kinoshita-lab/StemsMIDI/soft/StemsMIDI/src/stemsmidi_switch.hpp

#pragma once
#ifndef STEMSMIDI_SWITCH_HPP
#define STEMSMIDI_SWITCH_HPP

#include <cstdint>
#include <cstdlib>
#include <Arduino.h>
namespace kinoshita_lab
{
namespace stemsmidi
{

template <uint8_t num_switches, uint8_t scan_period>
class Switchs
{
public:
    typedef void (*SwitchHandler)(uint32_t switch_index, const int off_on);

    enum InternalState
    {
        Init,
        LoadStart,
        ReadEachBits,
        WaitNext,
        NumNormalStates,
        UnknownState = 0xff,
    };

    Switchs(
        const uint8_t npl_pin, const uint8_t clock_pin,
        const uint8_t output_pin, SwitchHandler handler = nullptr)
        : pins_(npl_pin, clock_pin, output_pin),
          handler_(handler)
    {

        // initialize switch status
        for (auto i = 0u; i < num_switches; ++i) {
            scan_buffers_[i]        = 1;
            former_scan_buffers_[i] = 1;
            switch_status_[i]       = 1;
        }
        pinMode(npl_pin, OUTPUT);
        pinMode(clock_pin, OUTPUT);
        pinMode(output_pin, INPUT_PULLUP);

        setState(Init);
    }

    void setHandler(SwitchHandler handler)
    {
        handler_ = handler;
    }

    virtual ~Switchs()
    {
    }

    void update()
    {
        switch (status_) {
        case Init:
            setState(LoadStart);
            break;
        case LoadStart:
            setState(ReadEachBits);
            break;
        case ReadEachBits: {
            for (auto ic_index = 0u; ic_index < num_switches / 8; ic_index++) {
                constexpr auto num_bits = 8;
                for (auto i = 0u; i < num_bits; ++i) {
                    digitalWrite(pins_.clock_pin, LOW);
                    const auto read_data                                    = digitalRead(pins_.output_pin);
                    scan_buffers_[(ic_index * num_bits) + num_bits - i - 1] = read_data;
                    digitalWrite(pins_.clock_pin, HIGH);
                }
            }
            updateSwitchStatus();
            setState(WaitNext);
            break;
        case WaitNext: {
            const auto current = millis();
            const auto delta   = current - wait_start_;
            if (delta >= scan_period) {
                setState(LoadStart);
            }
        } break;
        default:
            break;
        }
        }
    };

    void forceScan()
    {
        // scan 2 times just in case for robustness
        for (auto i = 0; i < 4; ++i) {
            for (auto i = 0; i < NumNormalStates; ++i) {
                update();
                delay(scan_period);
            }
        }
    }

    bool switchIsOn(const uint32_t switch_index) const
    {
        if (switch_index >= num_switches) {
            return false;
        }

        return switch_status_[switch_index] == 0;
    }

protected:
    uint8_t status_          = UnknownState;
    size_t will_read_switch_ = 0;

    void setState(const int status)
    {
        status_ = status;
        assert(pins_.npl_pin != Pins::INVALID_PIN_CONFIGURATION);
        assert(pins_.clock_pin != Pins::INVALID_PIN_CONFIGURATION);
        assert(pins_.output_pin != Pins::INVALID_PIN_CONFIGURATION);

        switch (status_) {
        case Init:
            digitalWrite(pins_.npl_pin, HIGH);
            digitalWrite(pins_.clock_pin, LOW);
            break;
        case LoadStart:
            digitalWrite(pins_.npl_pin, LOW);
            digitalWrite(pins_.clock_pin, LOW);
            will_read_switch_ = 0;
            break;
        case ReadEachBits:
            digitalWrite(pins_.clock_pin, LOW);
            digitalWrite(pins_.npl_pin, HIGH);
            break;
        case WaitNext:
            wait_start_ = millis();
            digitalWrite(pins_.npl_pin, HIGH);
            digitalWrite(pins_.clock_pin, LOW);
            break;
        default:
            break;
        }
    }

    void updateSwitchStatus()
    {
        for (auto i = 0u; i < num_switches; ++i) {
            if (scan_buffers_[i] == former_scan_buffers_[i]) {
                const auto new_status = scan_buffers_[i];
                auto current_status   = switch_status_[i];
                if (current_status != new_status) {
                    switch_status_[i] = (new_status);

                    const auto notification_status = !switch_status_[i]; // NOTE: inverted!! off = HIGH, on = LOW
                    if (handler_) {
                        (*handler_)(i, notification_status);
                    }
                }
            }
            former_scan_buffers_[i] = scan_buffers_[i];
        }
    }
    struct Pins
    {
        enum
        {
            INVALID_PIN_CONFIGURATION = 0xff,
        };
        Pins(const uint8_t npl_pin, const uint8_t clock_pin,
             const uint8_t input_pin)
            : npl_pin(npl_pin), clock_pin(clock_pin), output_pin(input_pin) {}

        Pins() = default;

        uint8_t npl_pin    = INVALID_PIN_CONFIGURATION;
        uint8_t clock_pin  = INVALID_PIN_CONFIGURATION;
        uint8_t output_pin = INVALID_PIN_CONFIGURATION;
    };
    Pins pins_;
    SwitchHandler handler_ = nullptr;

    uint8_t scan_buffers_[num_switches]        = {0};
    uint8_t former_scan_buffers_[num_switches] = {0};
    uint8_t switch_status_[num_switches]       = {0};
    uint32_t wait_start_                       = 0;

private:
    Switchs(const Switchs&) {}
};
} // namespace stemsmidi
} // namespace kinoshita_lab

#endif // STEMSMIDI_SWITCH_HPP
