kinoshita-lab/StemsMIDI/soft/StemsMIDI/src/stemsmidi_cc_numbers.h

#pragma once
#ifndef STEMSMIDI_CC_NUMBERS_H
#define STEMSMIDI_CC_NUMBERS_H

namespace kinoshita_lab
{
namespace stemsmidi
{
namespace cc_numbers
{
enum
{
    kDeckA_Slot1_Volume_Adjust = 10,
    kDeckA_Slot1_Mute_OnOff    = 11,
    kDeckA_Slot1_Filter_Adjust = 12,
    kDeckA_Slot1_Filter_OnOff  = 13,
    kDeckA_Slot1_FxSend_Adjust = 14,
    kDeckA_Slot1_FxSend_OnOff  = 15,

    kDeckA_Slot2_Volume_Adjust = 16,
    kDeckA_Slot2_Mute_OnOff    = 17,
    kDeckA_Slot2_Filter_Adjust = 18,
    kDeckA_Slot2_Filter_OnOff  = 19,
    kDeckA_Slot2_FxSend_Adjust = 20,
    kDeckA_Slot2_FxSend_OnOff  = 21,

    kDeckA_Slot3_Volume_Adjust = 22,
    kDeckA_Slot3_Mute_OnOff    = 23,
    kDeckA_Slot3_Filter_Adjust = 24,
    kDeckA_Slot3_Filter_OnOff  = 25,
    kDeckA_Slot3_FxSend_Adjust = 26,
    kDeckA_Slot3_FxSend_OnOff  = 27,

    kDeckA_Slot4_Volume_Adjust = 28,
    kDeckA_Slot4_Mute_OnOff    = 29,
    kDeckA_Slot4_Filter_Adjust = 30,
    kDeckA_Slot4_Filter_OnOff  = 31,
    kDeckA_Slot4_FxSend_Adjust = 32,
    kDeckA_Slot4_FxSend_OnOff  = 33,

    kDeckB_Slot1_Volume_Adjust = 40,
    kDeckB_Slot1_Mute_OnOff    = 41,
    kDeckB_Slot1_Filter_Adjust = 42,
    kDeckB_Slot1_Filter_OnOff  = 43,
    kDeckB_Slot1_FxSend_Adjust = 44,
    kDeckB_Slot1_FxSend_OnOff  = 45,

    kDeckB_Slot2_Volume_Adjust = 46,
    kDeckB_Slot2_Mute_OnOff    = 47,
    kDeckB_Slot2_Filter_Adjust = 48,
    kDeckB_Slot2_Filter_OnOff  = 49,
    kDeckB_Slot2_FxSend_Adjust = 50,
    kDeckB_Slot2_FxSend_OnOff  = 51,

    kDeckB_Slot3_Volume_Adjust = 52,
    kDeckB_Slot3_Mute_OnOff    = 53,
    kDeckB_Slot3_Filter_Adjust = 54,
    kDeckB_Slot3_Filter_OnOff  = 55,
    kDeckB_Slot3_FxSend_Adjust = 56,
    kDeckB_Slot3_FxSend_OnOff  = 57,

    kDeckB_Slot4_Volume_Adjust = 58,
    kDeckB_Slot4_Mute_OnOff    = 59,
    kDeckB_Slot4_Filter_Adjust = 60,
    kDeckB_Slot4_Filter_OnOff  = 61,
    kDeckB_Slot4_FxSend_Adjust = 62,
    kDeckB_Slot4_FxSend_OnOff  = 63,
};

} // namespace cc_numbers
} // namespace stemsmidi
} // namespace kinoshita_lab

#endif // STEMSMIDI_CC_NUMBERS_H
