kinoshita-lab/StemsMIDI/soft/StemsMIDI/src/stemsmidi_switch_ids.h

#pragma once
#ifndef STEMSMIDI_SWITCH_IDS_H
#define STEMSMIDI_SWITCH_IDS_H

namespace kinoshita_lab
{
namespace stemsmidi
{
enum SwitchId
{
    kSwitch_DeckA_Drums_Volume,
    kSwitch_DeckA_Drums_Filter,
    kSwitch_DeckA_Drums_FxSend,

    kSwitch_DeckA_Bass_Volume,
    kSwitch_DeckA_Bass_Filter,
    kSwitch_DeckA_Bass_FxSend,

    kSwitch_DeckA_Other_Volume,
    kSwitch_DeckA_Other_Filter,
    kSwitch_DeckA_Other_FxSend,

    kSwitch_DeckA_Vocals_Volume,
    kSwitch_DeckA_Vocals_Filter,
    kSwitch_DeckA_Vocals_FxSend,

    kSwitch_DeckB_Drums_Volume,
    kSwitch_DeckB_Drums_Filter,
    kSwitch_DeckB_Drums_FxSend,

    kSwitch_DeckB_Bass_Volume,
    kSwitch_DeckB_Bass_Filter,
    kSwitch_DeckB_Bass_FxSend,

    kSwitch_DeckB_Other_Volume,
    kSwitch_DeckB_Other_Filter,
    kSwitch_DeckB_Other_FxSend,

    kSwitch_DeckB_Vocals_Volume,
    kSwitch_DeckB_Vocals_Filter,
    kSwitch_DeckB_Vocals_FxSend,
};
} // namespace stemsmidi
} // namespace kinoshita_lab

#endif // STEMSMIDI_SWITCH_IDS_H
