kinoshita-lab/StemsMIDI/soft/StemsMIDI/src/stemsmidi_knob_ids.h

#pragma once
#ifndef STEMSMIDI_KNOBS_ID_H
#define STEMSMIDI_KNOBS_ID_H

namespace kinoshita_lab
{
namespace stemsmidi
{
enum KnobId
{
    kKnob_DeckA_Drums_Volume,
    kKnob_DeckA_Drums_Filter,
    kKnob_DeckA_Drums_FxSend,

    kKnob_DeckA_Bass_Volume,
    kKnob_DeckA_Bass_Filter,
    kKnob_DeckA_Bass_FxSend,

    kKnob_DeckA_Other_Volume,
    kKnob_DeckA_Other_Filter,
    kKnob_DeckA_Other_FxSend,

    kKnob_DeckA_Vocals_Volume,
    kKnob_DeckA_Vocals_Filter,
    kKnob_DeckA_Vocals_FxSend,

    kKnob_DeckB_Drums_Volume,
    kKnob_DeckB_Drums_Filter,
    kKnob_DeckB_Drums_FxSend,

    kKnob_DeckB_Bass_Volume,
    kKnob_DeckB_Bass_Filter,
    kKnob_DeckB_Bass_FxSend,

    kKnob_DeckB_Other_Volume,
    kKnob_DeckB_Other_Filter,
    kKnob_DeckB_Other_FxSend,

    kKnob_DeckB_Vocals_Volume,
    kKnob_DeckB_Vocals_Filter,
    kKnob_DeckB_Vocals_FxSend,
};
} // namespace stemsmidi
} // namespace kinoshita_lab

#endif // STEMSMIDI_KNOBS_ID_H
